bimac/Synkino/include/xbm.h

#pragma once

#define busybee_xbm_width  17
#define busybee_xbm_height 17
static const unsigned char busybee_xbm_bits[] U8X8_PROGMEM = {
  0x00, 0x00, 0xfe, 0x20, 0x00, 0xfe, 0x20, 0x78, 0xfe, 0x00, 0x8c, 0xfe,
  0xc0, 0x86, 0xfe, 0xc6, 0x42, 0xfe, 0x30, 0xa3, 0xfe, 0xb0, 0x55, 0xfe,
  0xc0, 0x0e, 0xfe, 0x70, 0x35, 0xfe, 0x98, 0x7f, 0xfe, 0x0c, 0x0d, 0xfe,
  0x84, 0xf6, 0xfe, 0x44, 0x36, 0xfe, 0xa4, 0xd4, 0xfe, 0x58, 0x50, 0xfe,
  0x00, 0x00, 0xfe};

#define play_xbm_width  9
#define play_xbm_height 9
static const unsigned char play_xbm_bits[] U8X8_PROGMEM = {
  0x03, 0x00, 0x0F, 0x00, 0x3F, 0x00, 0xFF, 0x00, 0xFF, 0x01, 0xFF, 0x00,
  0x3F, 0x00, 0x0F, 0x00, 0x03, 0x00};

#define pause_xbm_width  8
#define pause_xbm_height 8
static const unsigned char pause_xbm_bits[] U8X8_PROGMEM = {
  0xE7, 0xE7, 0xE7, 0xE7, 0xE7, 0xE7, 0xE7, 0xE7};

#define sync_xbm_width 20
#define sync_xbm_height 9
static const unsigned char sync_xbm_bits[] U8X8_PROGMEM = {
  0xFE, 0xFF, 0x07, 0xFF, 0xFF, 0x0F, 0xA7, 0xDA, 0x0C, 0xBB, 0x52, 0x0F,
  0x77, 0x4B, 0x0F, 0x6F, 0x5B, 0x0F, 0x73, 0xDB, 0x0C, 0xFF, 0xFF, 0x0F,
  0xFE, 0xFF, 0x07};

#define logo_xbm_width  96
#define logo_xbm_height 30
#define logo_xbm_x 14
#define logo_xbm_y 16
static const unsigned char logo_xbm_bits[] U8X8_PROGMEM = {
  0x00, 0x00, 0x00, 0x00, 0x00, 0x00, 0x00, 0xE0, 0xFF, 0xFF, 0xFF, 0x03,
  0x00, 0x1F, 0x00, 0xFE, 0xFF, 0xFF, 0xFF, 0x3F, 0x00, 0x00, 0x00, 0x0E,
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
#define ifma_xbm_x 30
#define ifma_xbm_y 46
static const unsigned char ifma_xbm_bits[] U8X8_PROGMEM = {
  0x5d, 0x64, 0xa0, 0x02, 0x40, 0xf8, 0xc5, 0x96, 0x10, 0x02, 0x40, 0xf8,
  0x4d, 0xf5, 0xb6, 0xb2, 0x70, 0xfd, 0x45, 0x94, 0x90, 0x52, 0x51, 0xf9,
  0x45, 0x94, 0x90, 0x54, 0x75, 0xfe};
